hanachi-ap/ergotonic_f24/acrylic/ergotonic_f24_v1r3_2_acrylic_cut.png

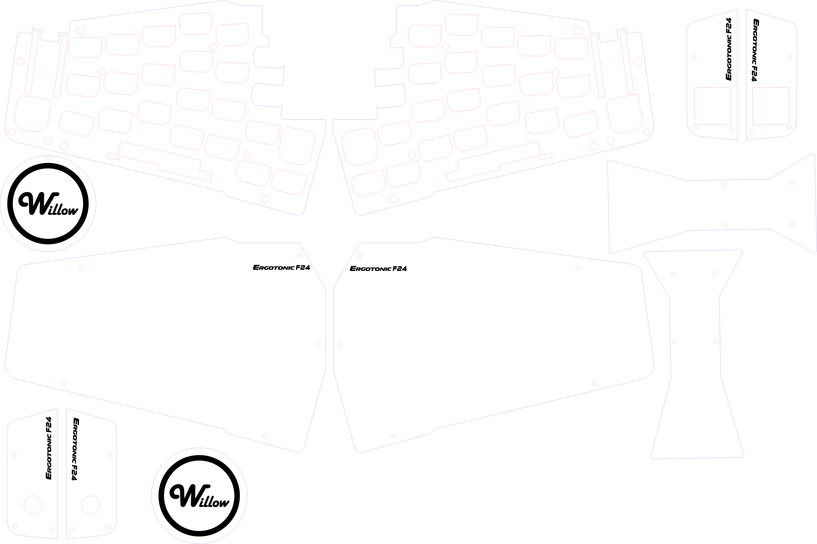
acrylic/ergotonic_f24_v1r3_2_acrylic_cut.png
