hanachi-ap/ergotonic_f24/docs/img/fig3_7_sh2.jpg

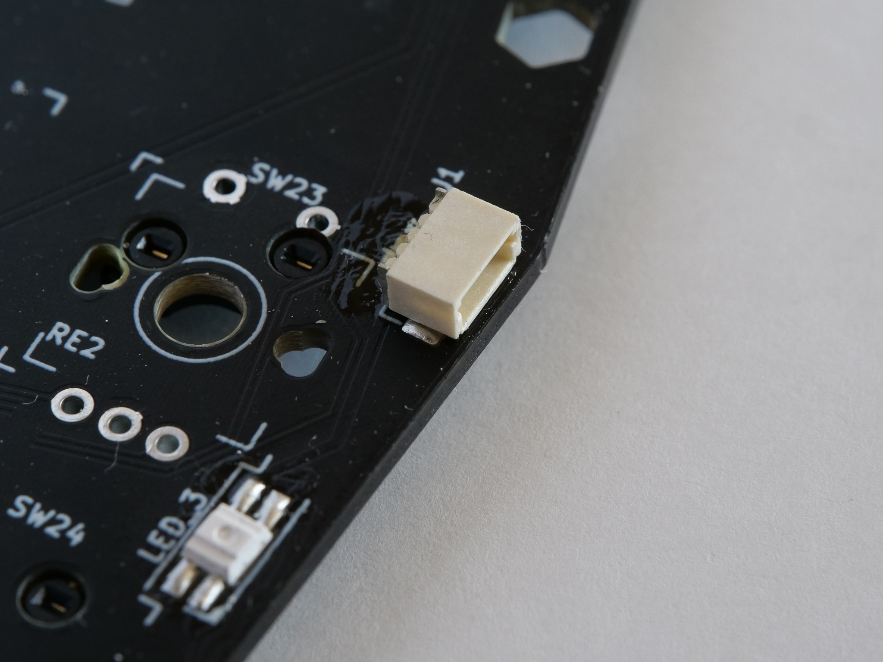
docs/img/fig3_7_sh2.jpg
