hanachi-ap/ergotonic_f24/docs/img/fig5_11.jpg

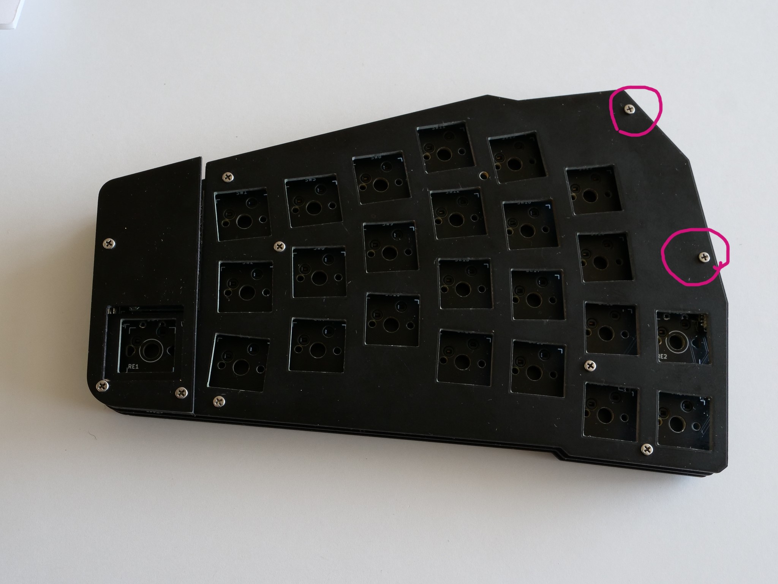
docs/img/fig5_11.jpg
