hanachi-ap/ergotonic_f24/docs/img/P1023473.jpg

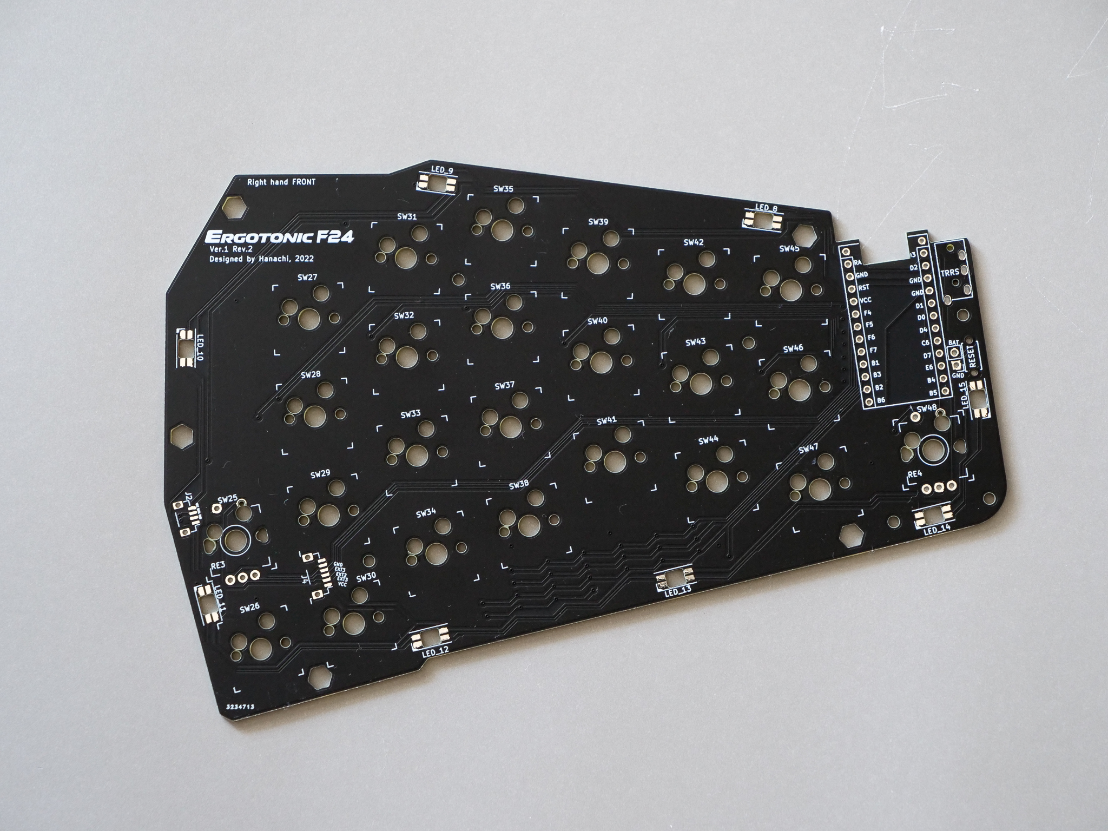
docs/img/P1023473.jpg
