hanachi-ap/ergotonic_f24/docs/img/P1023474.jpg

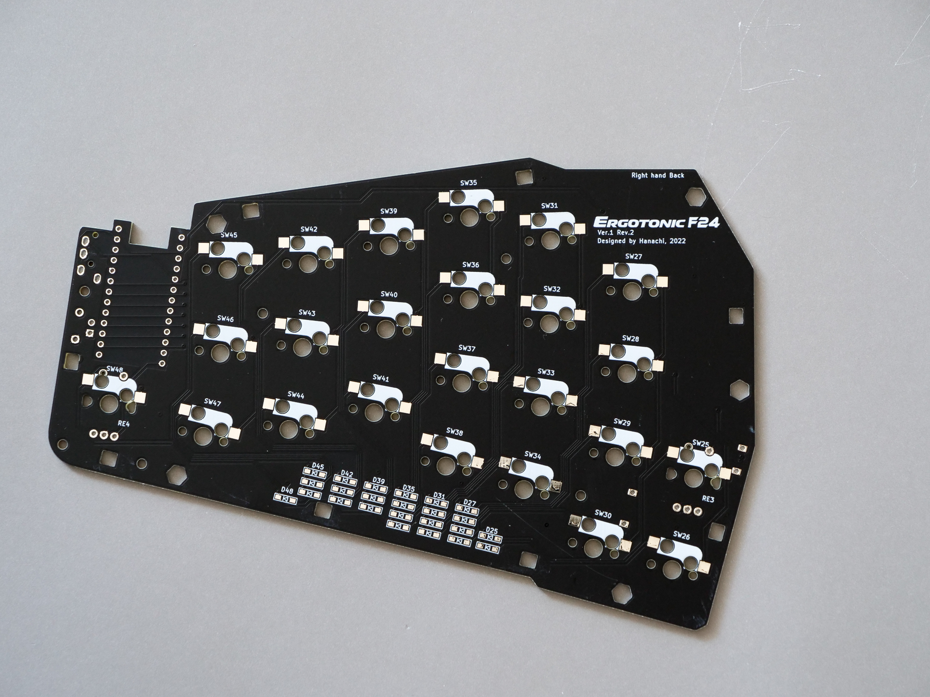
docs/img/P1023474.jpg
