hanachi-ap/ergotonic_f24/docs/img/P1023487.jpg

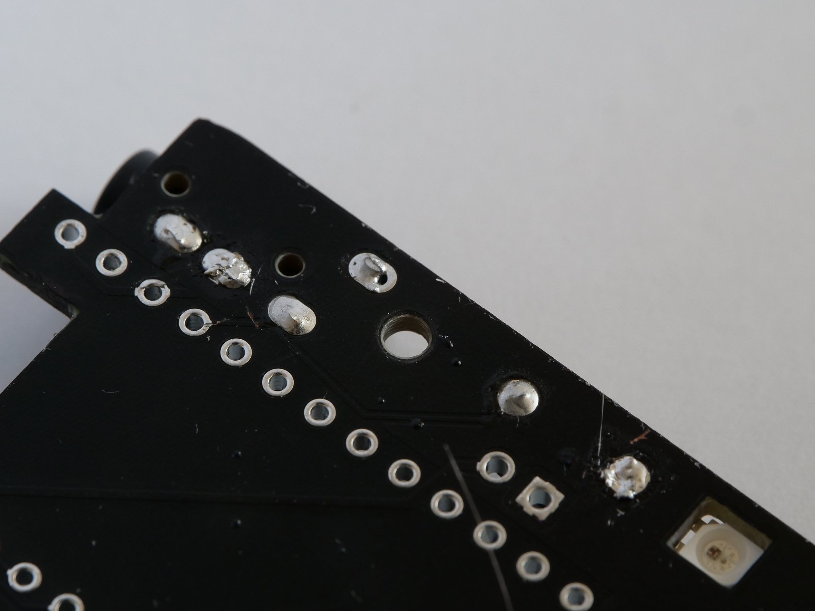
docs/img/P1023487.jpg
