hanachi-ap/ergotonic_f24/docs/img/P1023488.jpg

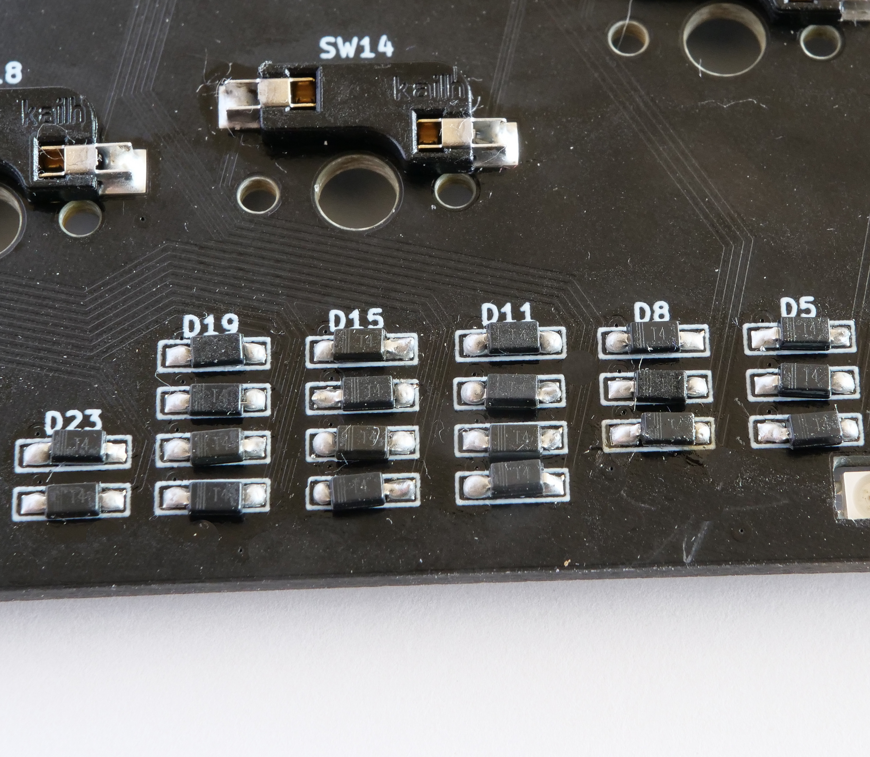
docs/img/P1023488.jpg
