hanachi-ap/ergotonic_f24/docs/img/P1023489.jpg

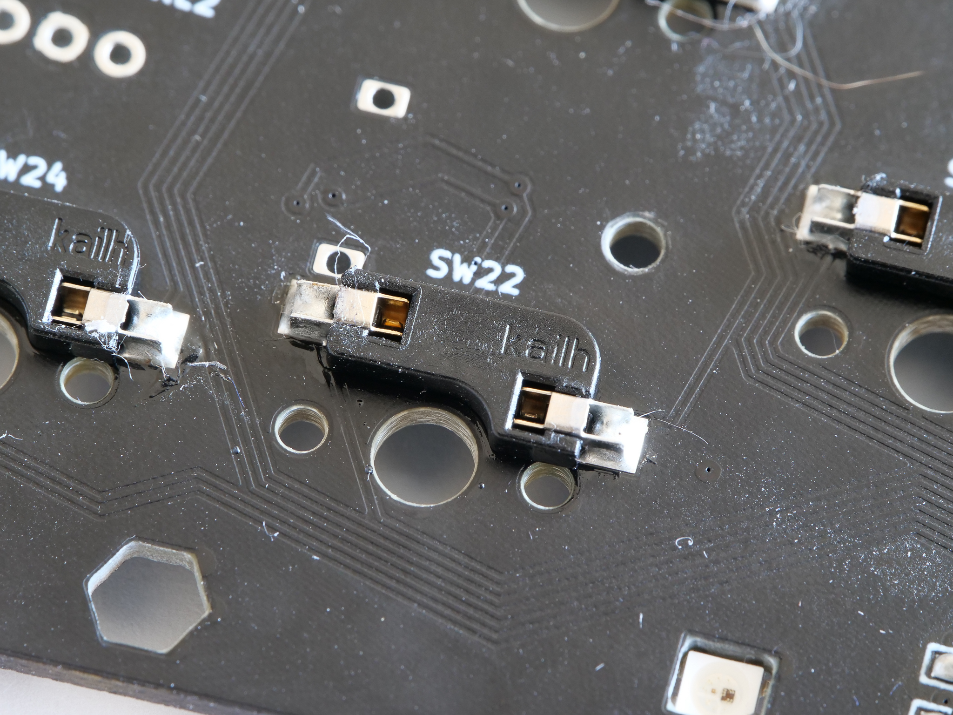
docs/img/P1023489.jpg
