hanachi-ap/ergotonic_f24/docs/img/P1023490.jpg

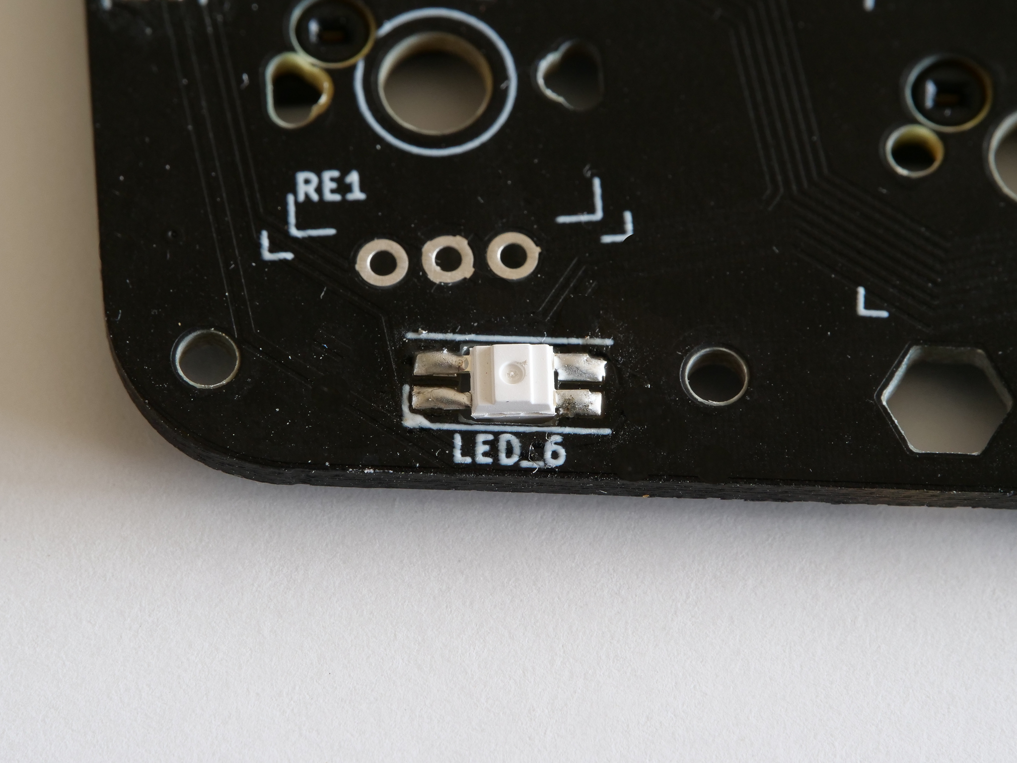
docs/img/P1023490.jpg
