hanachi-ap/ergotonic_f24/docs/img/P1023493.jpg

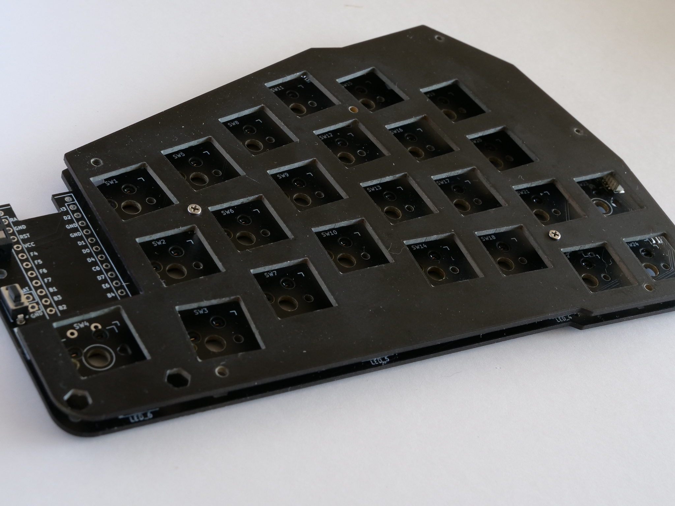
docs/img/P1023493.jpg
