hanachi-ap/ergotonic_f24/docs/img/P1023499.jpg

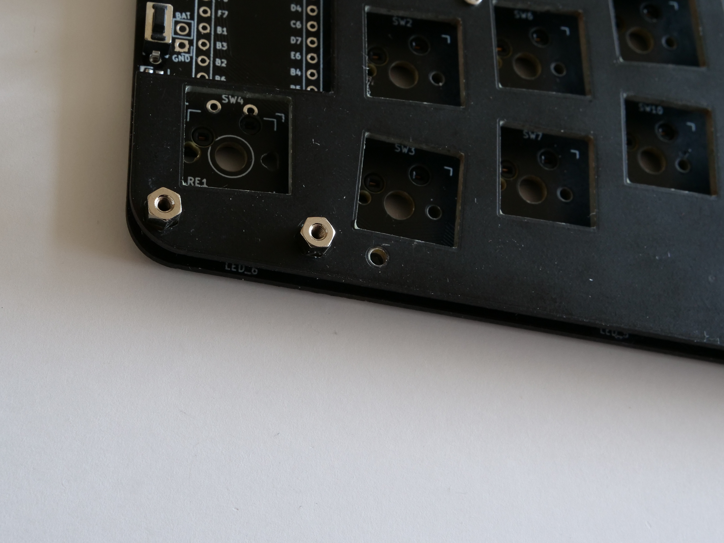
docs/img/P1023499.jpg
