hanachi-ap/ergotonic_f24/docs/img/P1023515.jpg

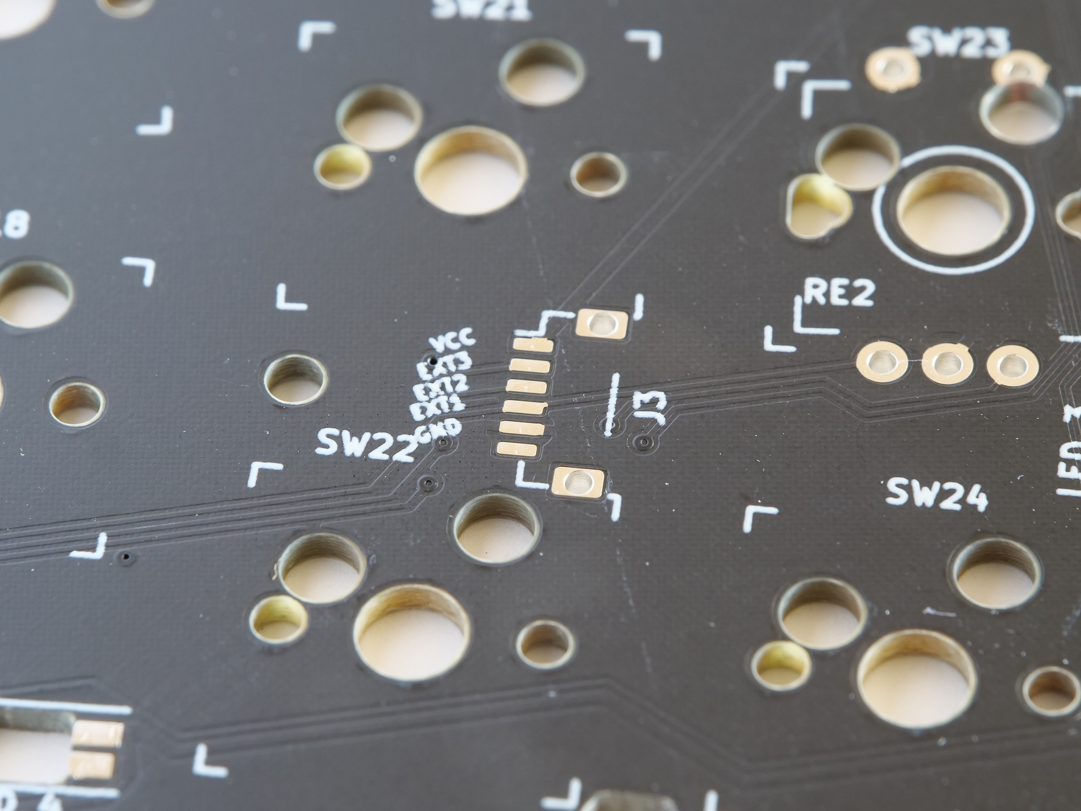
docs/img/P1023515.jpg
