hanachi-ap/ergotonic_f24/docs/img/P1023517.jpg

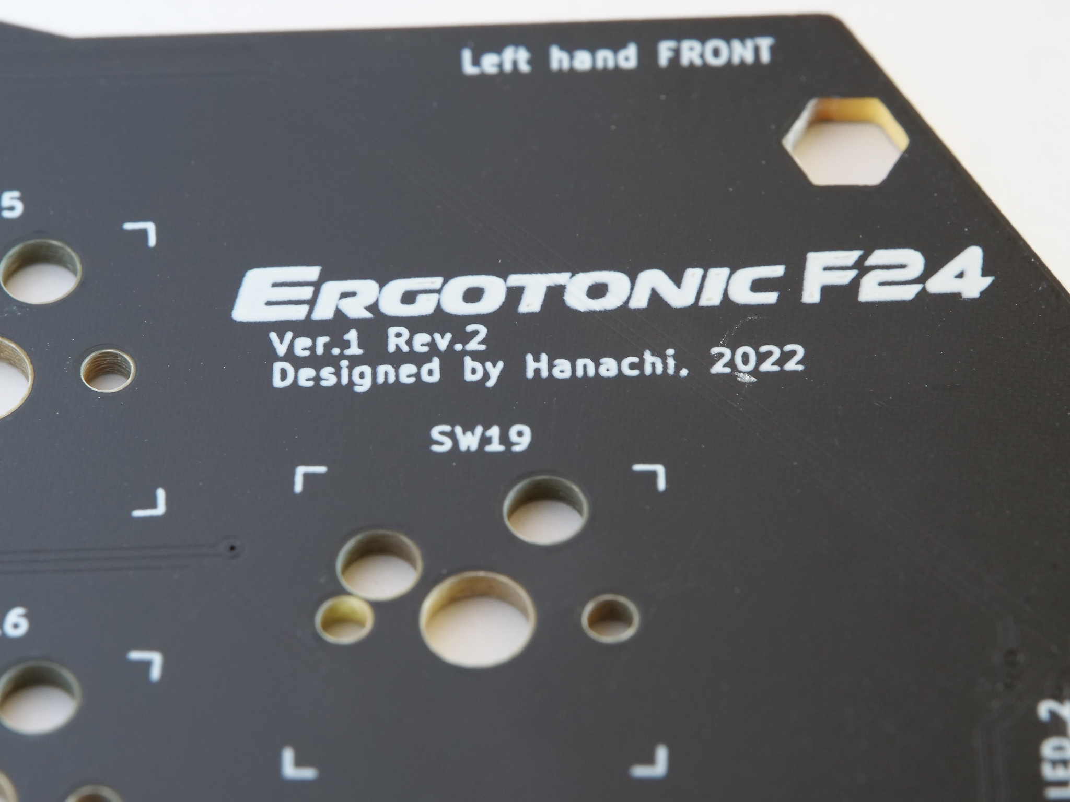
docs/img/P1023517.jpg
