hanachi-ap/ergotonic_f24/docs/img/P1023518.jpg

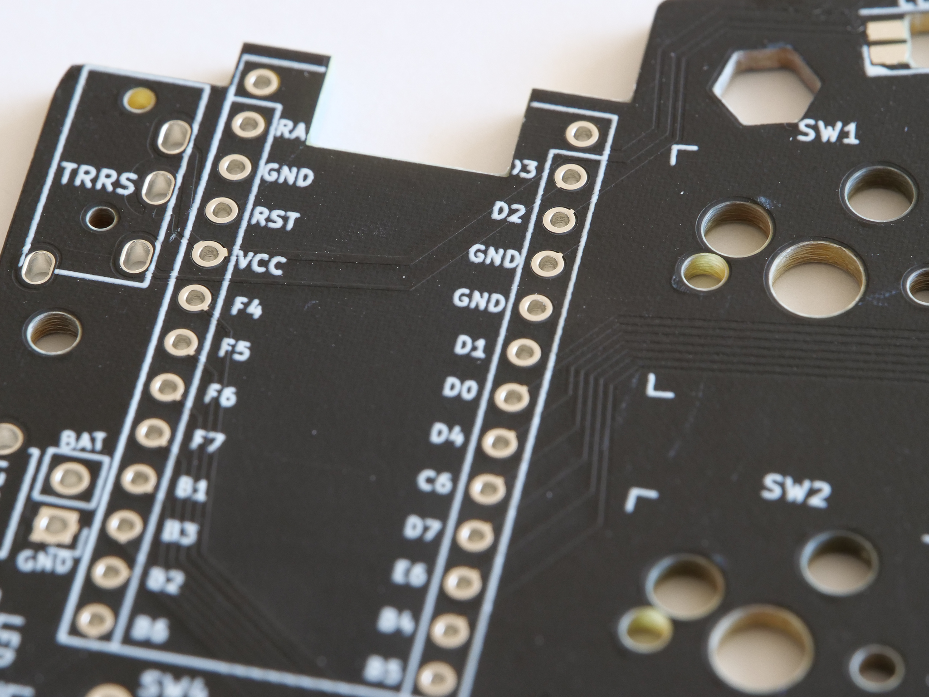
docs/img/P1023518.jpg
