hanachi-ap/ergotonic_f24/docs/img/qmk_toolbox.png

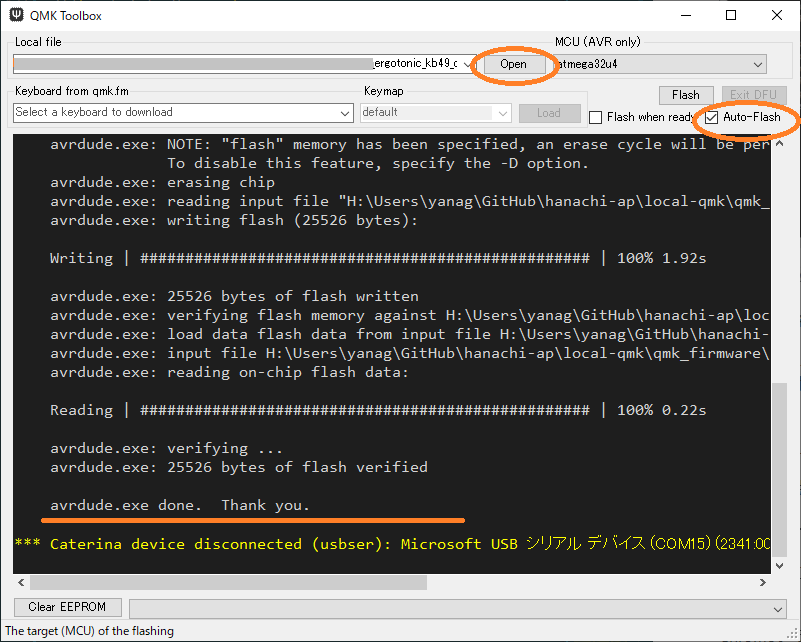
docs/img/qmk_toolbox.png
